NovaPrime18/nitride-nano/firmware/src/board.rs

//! Board constants and analog scaling (tune at bring-up).

/// Supply electrical limits (design targets).
pub const VOUT_MAX_MV: u32 = 60_000;
pub const VOUT_MIN_MV: u32 = 0;
pub const IOUT_MAX_MA: u32 = 20_000;
pub const POWER_MAX_MW: u32 = 240_000;

/// Input bus limits, supervised from the INA228 (rev2 input-side monitor).
/// These sit outside the PD contract itself and act as a firmware backstop on
/// top of the INA228 ALERT → SWITCH_EN hardware protection. The current limit
/// used at runtime is the active PD contract cap plus a small margin, falling
/// back to `IIN_MAX_MA` on a non-PD (XT90) input.
pub const VIN_MAX_MV: u32 = 58_000;
pub const IIN_MAX_MA: i32 = 22_000;
/// Headroom above the negotiated input-current cap before an input-overcurrent
/// fault is latched (covers measurement noise and transients).
pub const IIN_MARGIN_MA: i32 = 500;

/// NTC thermistor settings (matches PD240W-Firmware-example).
/// Circuit: 3.3V → R_PULLUP (4.7k) → NTC → GND, voltage at junction.
pub const NTC_BETA: f32 = 3950.0;
pub const NTC_R25_OHM: f32 = 10_000.0;
pub const NTC_PULLUP_OHM: f32 = 4_700.0;
pub const NTC_OVERTEMP_C: i32 = 80;
// TODO(dead-code): derating threshold carried over from the PD240W example, but no
// thermal-derating logic exists in this firmware yet, so nothing reads it.
// Preserved for when graduated derating is implemented.
// pub const NTC_DERATE_START_C: i32 = 70;

// TODO(dead-code): graduated temperature thresholds from the PD240W example AppConfig.
// Only NTC_OVERTEMP_C is actually enforced (see control::supply); these graduated
// levels are never referenced. Preserved for a future UI/derating feature.
// pub const TEMP_CAUTION_C: i32 = 50;
// pub const TEMP_WARNING_C: i32 = 65;
// pub const TEMP_CRITICAL_C: i32 = 75;
// pub const TEMP_SHUTDOWN_C: i32 = 80;

/// ADC full-scale reference (VREF+ = VDDA unless VREFBUF used for DAC only).
pub const ADC_VREF_MV: u32 = 3300;
// TODO(dead-code): misleading leftover — all ADCs run at 12-bit resolution and every
// scaling path in `sense::adc_sense` divides raw counts by 4096. Nothing references
// this 16-bit "oversampled" constant.
// pub const ADC_MAX: u32 = 65535; // 16-bit oversampled

/// Divider ratios: physical = adc_counts * SCALE / 4096 (12-bit ADC)
/// TODO: derive from Converter.kicad_sch resistor networks.
pub const VOUT_SENSE_NUM: u32 = 85_140; // mV at full scale (248k/10k divider, 3.3V ref)
/// ISMON monitor gain at the PA3 node, in mV per amp. The LT8390A datasheet
/// gives `V_ISMON = 10 · V(ISP−ISN) + V_OFFSET`, and the board's output-current
/// shunt is R18 = 2 mΩ, so the gain is `10 · 2 mΩ = 20 mV/A`. This is a
/// datasheet-derived value, not a per-board trim: verify it against a known load
/// (a shunt swap scales it directly) before changing it.
pub const ISENSE_MV_PER_A: u32 = 20;

/// Zero-current ISMON voltage at the PA3 node, in mV — the per-board offset
/// calibration.
///
/// The LT8390A offset is only specified to 0.20–0.30 V while the current signal
/// is 20 mV/A, so the full 100 mV spread is 5 A of error. Even the 5 mV residual
/// left by a near-typical part is 0.25 A on the display at *every* load — which
/// is what the 2026-09-25 bench run showed (readings low by ~0.25 A from 0.25 A
/// to 2.5 A).
///
/// MEASURE IT WITH THE OUTPUT **ENABLED** AND NO LOAD. The LT8390A's ISMON
/// buffer is powered down with the rest of the chip while `EN/UVLO` is low, so
/// the level read with the converter parked is not the operating offset. The
/// previous firmware learned the zero at boot with the converter disabled; that
/// is why the calibration never took. This constant replaces that learn.
///
/// Bench procedure: enable the output with no load, read the `isense:` RTT line
/// (`raw … mV`), or DMM the ISMON node / R49, and set this to that value. The
/// value below was fitted from the 2026-09-27 bench run: with the converter
/// enabled and no load, PA3 read raw 307–308 counts = 247–248 mV on this board,
/// so the previous 244 mV constant showed ~200–250 mA at true zero and carried
/// that offset up through the whole range.
pub const ISENSE_ZERO_MV: u32 = 248;
pub const VBUS_SENSE_NUM: u32 = 69_600;

/// DAC 12-bit. The DAC reference is VREF+, which this board ties to +3V3 (the
/// internal VREFBUF is left high-impedance in `main`), so the full-scale
/// reference is the 3.3 V rail rather than the 2.5 V VREFBUF setting.
pub const DAC_MAX_CODE: u16 = 4095;
pub const DAC_VREF_MV: u32 = 3300;

/// CV feedback network (Converter sheet, U1 = LT8390A). The FB pin is a
/// current-summing node:
///
/// ```text
///   VOUT ── R19 ──┬── R20 ── GND
///                 │
///   CV_Set ─ R36 ─┴── FB
/// ```
///
/// The LT8390A regulates FB to [`CV_FB_REF_MV`] (1.000 V typ), so summing the
/// currents into FB gives the open-loop (inverted) control law
///
/// ```text
///   V_OUT = CV_FB_REF_MV·(1 + R19/R36 + R19/R20) − V_DAC·(R19/R36)
/// ```
///
/// with `V_DAC = DAC_VREF_MV · code / DAC_MAX_CODE`. These resistor values are
/// the source of truth for the CV map — `control::dac_cv` derives the
/// setpoint→code mapping from them analytically. (A previous hand-entered
/// calibration table did not match this network: it assumed ~13.5 mV/code while
/// the network gives ~28.8 mV/code, so the real output tracked ~1.9× the
/// setpoint with an offset.)
pub const CV_FB_REF_MV: u32 = 1_000; // LT8390A FB regulation (1.00 V typ)
pub const CV_FB_TOP_OHM: u32 = 357_000; // R19, VOUT → FB
pub const CV_FB_BOTTOM_OHM: u32 = 10_000; // R20, FB → GND
pub const CV_SUM_OHM: u32 = 10_000; // R36, CV_Set → FB

/// Max CV DAC code change per supply tick (see `control::dac_cv::CvDac::slew`).
/// The supply tick is 1 ms, so this is N LSB per ms (~N*1000 LSB/s). Tune down
/// for a gentler ramp if output-stage ringing/FET heating persists.
pub const CV_SLEW_MAX_LSB_PER_TICK: u16 = 4;

/// How often the supply supervisor prints its consolidated `supply:` diagnostic.
/// One second gives a slow enough scroll to read while still catching a fault or
/// mode change within a second of the event; edge-triggered events (faults, a
/// binding power cap, a CV↔CC transition) are logged immediately regardless.
pub const SUPPLY_LOG_MS: u64 = 1_000;

/// Supply-snapshot period while the output is out of regulation (below
/// [`VOUT_SAG_PCT`] of the setpoint). A converter saturation/collapse can be
/// short-lived, so the 1 s cadence misses the interesting part; this tightens it
/// and a dedicated edge line records the transition either way.
pub const SUPPLY_LOG_SAG_MS: u64 = 200;

/// An enabled output below this percentage of its setpoint is reported as a CV
/// regulation failure (the LT8390A is not holding FB at 1 V), as opposed to a
/// deliberate current limit.
pub const VOUT_SAG_PCT: u32 = 85;

/// Advisory threshold on the commanded step-down ratio `VIN/VOUT`, in percent.
///
/// The 2026-09-27 bench run showed this board cannot hold regulation above
/// roughly 70 W when run at 48 V in / 12 V out (`VIN/VOUT = 4.0`) — it sags and
/// "chitters" — while the *same* hardware reached its full 10 A programmed CC
/// limit at 28 V in (`VIN/VOUT = 2.3`). That is the high-step-down / low-duty
/// corner (1 MHz from R1 = 147 k, with a 2.2 µH inductor and the LSP/LSN filter
/// as built). A one-shot `supply:` warning is emitted above this ratio so a
/// marginal rail is visible in the log instead of looking like a firmware bug.
/// Prefer the lowest PD rail that is still a clean buck (`control::auto_track`
/// already does this in Auto mode).
pub const DEEP_BUCK_WARN_RATIO_PCT: u32 = 300;

/// The measured output current must exceed the commanded limit by this much
/// before the software over-current fault latches. The ISMON path is only
/// specified to ±3 %, its offset is part-specific (see `ISENSE_ZERO_MV`), and
/// the observed bias on the bench was ~0.6 A — which is >5 % of a 3 A limit.
/// The hardware CC loop is the primary limit; this is a runaway backstop, so a
/// generous margin is correct. 115 % still sits below the 20 A design cap for
/// every limit below ~17 A and the absolute `IOUT_MAX_MA` check covers the top.
pub const IOUT_TRIP_MARGIN_PCT: u32 = 115;

// ---------------------------------------------------------------------------
// LT8390A output-current-limit input (CTRL pin) network
// ---------------------------------------------------------------------------
//
// The CC DAC does NOT drive the LT8390A CTRL pin directly. On the board,
//
//     PA6 / CC_Set ── R48 ──┬── CTRL (U1 pin 10)
//                           │
//     LT8390A VREF ── R5 ───┤
//                           │
//                          R4
//                           │
//                          GND
//
// so CTRL is a resistor-summing node:
//
//     V_CTRL = k · V_DAC + V_ctrl0
//     k       = (R4 || R5) / (R48 + (R4 || R5))
//     V_ctrl0 = VREF · R4 / (R4 + R5)
//
// `control::dac_cc` inverts this to turn a requested current limit into a DAC
// code (and reports the limit a code actually produces), and `control::supply`
// logs both so a divider mismatch is visible instead of silent.
//
// NOTE (rev2 fitted values): R48 = 10 k, R5 = 357 k, R4 = 75 k. R5 was raised
// from 124 k to 357 k as the "DAC high-Z / MCU held in reset" fail-safe: with
// the DAC floated, V_CTRL = VREF·R4/(R4+R5) ≈ 0.347 V, i.e. ≈ 4.9 A, instead of
// ≈ 25 A with 124 k. **If the next board revision changes this divider, update
// these three constants or every CC limit will be wrong.**
pub const LT8390_VREF_MV: u32 = 2_000; // LT8390A VREF pin (NOT the 1.0 V FB ref)
pub const CTRL_SERIES_OHM: u32 = 10_000; // R48, CC_Set → CTRL
pub const CTRL_VREF_OHM: u32 = 357_000; // R5,  VREF    → CTRL
pub const CTRL_GND_OHM: u32 = 75_000; // R4,  CTRL    → GND

/// LT8390A CTRL→current-limit transfer, from the datasheet:
///
/// ```text
///   V(ISP−ISN)_threshold = (V_CTRL − 0.25 V) · 0.1     (0.3 V ≤ V_CTRL ≤ 1.15 V)
///   I_LIMIT              = V(ISP−ISN)_threshold / R18
/// ```
///
/// so with the R18 = 2 mΩ output shunt, `I_LIMIT(mA) = (V_CTRL(mV) − 250) · 50`.
/// The transfer saturates at `V_CTRL ≥ 1.35 V` (100 mV ⇒ 50 A) and the part
/// latches switching off below [`LT8390_CTRL_LATCHOFF_MV`] — which is why the
/// disabled path's CC code of 0 is a genuine shutdown, not just a low limit.
pub const LT8390_CTRL_OFFSET_MV: u32 = 250;
/// Sense-threshold volts per volt of CTRL, scaled ×1000 (0.1 V/V).
pub const LT8390_CTRL_SLOPE_MILLI: u32 = 100;
/// Output current shunt R18, in milliohms.
pub const ISENSE_SHUNT_MOHM: u32 = 2;
/// Below this CTRL voltage the LT8390A stops switching (latch-off, 285–315 mV).
pub const LT8390_CTRL_LATCHOFF_MV: u32 = 300;

// ---------------------------------------------------------------------------
// Achievable CC-limit range (the part's CTRL window, not the firmware's choice)
// ---------------------------------------------------------------------------
//
// The datasheet's CTRL → ISP/ISN threshold transfer is three regions:
//
//   0.30 V ≤ V_CTRL ≤ 1.15 V   linear,  threshold 5 mV → 90 mV
//   1.15 V ≤ V_CTRL ≤ 1.35 V   smooth transition 90 mV → 100 mV
//           V_CTRL ≥ 1.35 V   constant 100 mV full scale
//           V_CTRL < 0.30 V   stops switching (latch-off)
//
// so the part can command a **20:1** current window (5 → 100 mV), and no single
// shunt value can reach below `CC_MIN_MA`. With the fitted R18 = 2 mΩ that is
// 2.5 A … 50 A. The low end sits exactly on the latch-off, hence the settable
// floor below.

/// Sense-threshold window endpoints, in mV across R18.
pub const LT8390_CTRL_MIN_SENSE_MV: u32 = 5;
pub const LT8390_CTRL_LINEAR_MAX_SENSE_MV: u32 = 90;
pub const LT8390_CTRL_MAX_SENSE_MV: u32 = 100;
/// CTRL voltages where the window is linear-top / saturated, in mV.
pub const LT8390_CTRL_LINEAR_TOP_MV: u32 = 1_150;
pub const LT8390_CTRL_SAT_MV: u32 = 1_350;

/// Smallest / largest current limit the fitted shunt can **sustain** (`mV/mΩ = A`,
/// so `sense_mV · 1000 / R18_mΩ` is mA). With R18 = 2 mΩ: 2.5 A … 50 A. The low
/// end is the exact latch-off and is only reachable once the stage is already
/// switching — see [`CC_SET_MIN_MA`] for the cold-start floor.
pub const CC_MIN_MA: u32 = LT8390_CTRL_MIN_SENSE_MV * 1_000 / ISENSE_SHUNT_MOHM;
pub const CC_MAX_MA: u32 = LT8390_CTRL_MAX_SENSE_MV * 1_000 / ISENSE_SHUNT_MOHM;

/// CTRL voltage needed to *leave* latch-off: the falling-threshold worst case
/// (315 mV) plus the 25 mV hysteresis.
///
/// This is the trap in the low end of the CC range. The part can *sustain* a
/// limit down at `LT8390_CTRL_LATCHOFF_MV` (0.30 V → 2.5 A) **once it is
/// switching**, but from a cold start it will not begin switching until CTRL
/// exceeds ~0.34 V. That is why the 2026-09-28 CV run held ~2.5 A while a CC
/// cold start would not hold below ~6 A — start-vs-sustain, not a map error.
pub const LT8390_CTRL_LATCHOFF_MAX_MV: u32 = 315;
pub const LT8390_CTRL_LATCHOFF_HYST_MV: u32 = 25;
pub const LT8390_CTRL_START_MV: u32 =
    LT8390_CTRL_LATCHOFF_MAX_MV + LT8390_CTRL_LATCHOFF_HYST_MV;
/// Datasheet-guaranteed cold-start floor (`(340 − 250) mV / 2 mΩ` = 4.5 A).
pub const CC_START_MIN_MA: u32 =
    (LT8390_CTRL_START_MV - LT8390_CTRL_OFFSET_MV) * 100 / ISENSE_SHUNT_MOHM;

/// Bench-measured CC current offset: near the low end the loop delivers this
/// much *more* current than commanded. On the 2026-09-28 board, setting 0.1 A
/// drew 3.75 A and 0.2 A drew 3.85 A — a clean 1:1 slope with a **+3.65 A
/// intercept**, i.e. a CTRL / ISP-ISN offset near latch-off, not a DAC map
/// error. `dac_cc` cancels it here so the number on the I-LIM screen is the
/// current actually drawn. Re-measure at mid-range before trusting it across
/// the whole range: a 10 A run on 2026-09-27 tracked to <1 %, so the offset is
/// known to fade at high current.
pub const CC_CURRENT_OFFSET_MA: u32 = 3_650;

/// Settable CC-range floor: the offset above plus a 0.1 A command, so the lowest
/// setting (3.75 A here) is the lowest current the loop can actually deliver.
/// Because the setpoint now means the *actual* current, the range reads
/// 3.75 A … 20 A rather than 0.1 A … 20 A.
pub const CC_SET_MIN_MA: u32 = CC_CURRENT_OFFSET_MA + 100;
/// Settable CC-range ceiling (design max; the chip itself would allow 50 A).
pub const CC_SET_MAX_MA: u32 = IOUT_MAX_MA;

/// I2C addresses
pub const TPS26750_ADDR: u8 = 0x21;
pub const SSD1306_ADDR: u8 = 0x3C;
pub const CAT24C512_ADDR: u8 = 0x50;
/// INA228 input power monitor on the PD bus (A0 = A1 = GND).
pub const INA228_ADDR: u8 = 0x40;

/// INA228 scaling. R60 = 8 mΩ on the input bus; 20 A × 8 mΩ = 160 mV, which
/// fits the ±163.84 mV `ADCRANGE = 0` shunt range with ~2 % headroom.
pub const INA228_SHUNT_MOHM: u32 = 8;
pub const INA228_MAX_CURRENT_MA: u32 = IOUT_MAX_MA;
/// CONFIG: ADCRANGE = 0 (±163.84 mV), shunt temperature compensation off.
pub const INA228_CONFIG: u16 = 0x0000;
/// ADC_CONFIG: MODE = 0xF (continuous bus + shunt + temperature), 1052 µs per
/// conversion, AVG = 16 → ~50 ms per full update. Sample it every 100 ms.
pub const INA228_ADC_CONFIG: u16 = 0xFB6A;
/// SHUNT_CAL = 13107.2e6 × CURRENT_LSB × R_shunt with
/// CURRENT_LSB = 20 A / 2^19 = 38.147 µA and R_shunt = 8 mΩ → 4000.
pub const INA228_SHUNT_CAL: u16 = 4_000;

/// Auto-tracking PD rail selection.
///
/// The LT8390A only leaves its 4-switch buck-boost region when `VIN/VOUT` is at
/// least ~1.33 (clean buck) or at most ~0.75 (clean boost); the peak-buck/peak-
/// boost crossover sits at 0.98–1.04. These percentages add a small guard band
/// on top of the datasheet typical thresholds. They are the tuning knobs for
/// the bench efficiency sweep: lower them to allow rails closer to the
/// transition, raise them for more margin.
pub const AUTO_TRACK_BUCK_MIN_RATIO_PCT: u32 = 135;
pub const AUTO_TRACK_BOOST_MAX_RATIO_PCT: u32 = 70;
/// Delivered-power headroom required of a candidate rail before it is accepted
/// (`rail_mw >= requested_mw * pct / 100`), covering conversion losses.
pub const AUTO_TRACK_POWER_HEADROOM_PCT: u32 = 110;
/// A setpoint must be stable this long before a rail change is commanded, and
/// two rail changes are never closer together than the interval below.
pub const AUTO_TRACK_SETTLE_MS: u64 = 300;
pub const AUTO_TRACK_MIN_INTERVAL_MS: u64 = 1_000;
/// Park the converter while the input rail is renegotiated. The LT8390A copes
/// with VIN steps, but a PD source can momentarily drop VBUS to 5 V during a
/// re-request, so the output is briefly disabled to protect the stage.
pub const AUTO_TRACK_DISABLE_DURING_SWITCH: bool = true;

/// Highest SPR contract voltage. A rail above this can only be obtained by
/// entering EPR mode; the TPS26750 attempts EPR on its own once a request
/// window above this is allowed and the loaded sink configuration declares EPR
/// PDOs. Keep in step with `0x33` / `0x37` of `config_TPS26750_*_fullFlash.c`.
pub const SPR_MAX_MV: u32 = 20_000;
/// Fixed EPR rails the sink configuration declares (`0x33` PDOs 8-10). The
/// source's own EPR PDOs are invisible in `RX_SOURCE_CAPS` until EPR mode has
/// been entered, so [`crate::pd::auto_track`] injects these as candidates when
/// the output setpoint cannot be served from SPR alone.
pub const EPR_RAILS_MV: [u32; 3] = [28_000, 36_000, 48_000];
/// Current assumed for an injected EPR rail (EPR fixed PDOs carry 5 A).
pub const EPR_RAIL_CURRENT_MA: u32 = 5_000;
/// EPR AVS APDO window declared by the sink configuration (`0x33` PDO 11).
///
/// Before EPR mode has been entered, an above-SPR rail is requested as an **EPR
/// AVS** contract inside this window: asserting `EPR AVS Enable Sink Mode`
/// (0x37 bit 128) is what makes the controller attempt EPR mode entry (TRM
/// Table 4-21), and SDAA265 §5.3 makes a bare fixed >20 V window fall back to
/// 5 V. Once EPR is entered and the source advertises its own EPR PDOs, a
/// specific above-SPR preset is requested as a **fixed** EPR PDO through
/// `Tps26750::request_fixed_epr_rail` instead (see `PD_ROOT_CAUSE.md`).
/// Keep in step with `0x33`/`0x37` of the config image.
pub const EPR_AVS_MIN_MV: u32 = 15_000;
pub const EPR_AVS_MAX_MV: u32 = 48_000;

/// How long to keep the converter output disabled after an EPR request before
/// loading it. Some sources are still settling VBUS through the 20→28/48 V
/// transition; enabling the load then can dip VBUS enough to brown the board
/// out. Two chargers did this at 28 V while a powerbank at the same voltage did
/// not, so this is a ride-through window, not a fixed voltage limit.
pub const EPR_SETTLE_MS: u64 = 800;
/// USB-PD SPR PPS is only defined inside this window; a manual preset that
/// lands here with no matching fixed PDO is served by a PPS contract.
pub const PPS_MIN_MV: u32 = 3_300;
pub const PPS_MAX_MV: u32 = 21_000;
/// A preset this close to a fixed PDO uses the fixed PDO instead of PPS.
pub const PPS_FIXED_PREFER_MV: u32 = 1_000;

/// Converter disable: active level (verify on bench vs LT8390 RUN).
pub const CONVERTER_DISABLE_ACTIVE_HIGH: bool = true;

/// UI timing
pub const DEBOUNCE_MS: u64 = 25;
/// Max gap between two encoder-button presses that counts as a double click.
/// The single-click action (VSET mode on the Main screen) is deferred by this
/// long so a double click can be recognised instead; it comfortably exceeds
/// `DEBOUNCE_MS` while staying short enough that entering VSET mode still feels
/// immediate.
pub const ENC_DOUBLE_CLICK_MS: u64 = 350;
/// Quadrature counts per encoder detent. `Qei::new` configures the timer for
/// X4 decoding (`Sms::ENCODER_MODE_3`). The fitted encoder produces a detent
/// every two counts (measured: one detent used to fire two `EncTurn` events, and
/// dividing by 4 made the knob half-speed). Raw counts are divided by this so
/// every screen receives one event per detent.
pub const ENCODER_COUNTS_PER_DETENT: i32 = 2;
pub const UI_REFRESH_MS: u64 = 80;
pub const INPUT_POLL_MS: u64 = 5;
pub const SUPPLY_TICK_MS: u64 = 1;
pub const ADC_SAMPLE_MS: u64 = 2;
/// INA228 refresh period. Must be longer than the chip's ~50 ms conversion
/// cycle (ADC_CONFIG above) or reads return overlapping samples.
pub const INA228_POLL_MS: u64 = 100;

// ---------------------------------------------------------------------------
// Status LED (D31 on PA15)
// ---------------------------------------------------------------------------

/// Status LED wiring: `PA15 → D31 (anode → cathode) → R81 → GND`, so PA15
/// HIGH lights it — **active high**. PA15 is `TIM2_CH1`; TIM2 is otherwise
/// unused (TIM4 is the encoder QEI, TIM15 is the Embassy time driver), so the
/// LED is driven as hardware PWM and can be dimmed precisely.
pub const LED_PWM_HZ: u32 = 1_000;

/// LED task tick. Only the on/off *envelope* is quantised to this; the
/// brightness inside an "on" phase is set by the PWM duty, so the heartbeat
/// stays dim and steady even at this tick rate.
pub const LED_TICK_MS: u64 = 5;

/// PWM duty for the healthy heartbeat pulses. Low enough to read as "very dim"
/// next to the full-brightness error codes — tune to taste on the bench.
pub const LED_HEARTBEAT_DUTY_PCT: u8 = 3;

/// PWM duty for fault/error code flashes (full brightness, hard to miss).
pub const LED_FAULT_DUTY_PCT: u8 = 100;

/// PWM duty for the in-progress (EEPROM activity) pulse.
pub const LED_ACTIVITY_DUTY_PCT: u8 = 35;

/// Report "INA228 missing" / "PD controller lost" / "PD no rail" as blink
/// codes. Set false to limit the LED to latched faults + EEPROM status, which
/// is what a build without those parts fitted wants.
pub const LED_SUBSYSTEM_CODES: bool = true;

/// Suppress the INA228 / PD-controller "missing" codes for this long after
/// boot. Both subsystems are probed asynchronously and are legitimately absent
/// for the first moments of a power-up, so the LED would otherwise flash a
/// code on a perfectly healthy boot.
pub const LED_SUBSYSTEM_GRACE_MS: u64 = 4_000;

/// CFG menu → "Output V sweep": 32 points evenly spaced from 10 V to 56 V,
/// inclusive at both ends (31 intervals, ≈1.48 V/step), each held for 2 s
/// (~64 s total).
///
/// NOTE: `control::dac_cv::CvDac::mv_to_code` derives its map from the FB
/// network, whose code-0 output is well above 60 V, so every sweep point is
/// reached without clamping. `VOUT_MAX_MV` is 60 V, so the supply supervisor's
/// 105 % overvoltage guard never trips on a sweep.
pub const SWEEP_START_MV: u32 = 10_000;
pub const SWEEP_END_MV: u32 = 56_000;
/// Number of points in one sweep (inclusive of both endpoints).
pub const SWEEP_POINTS: u8 = 32;
/// Dwell time per sweep point.
pub const SWEEP_STEP_MS: u64 = 2_000;

/// Sweep efficiency diagnostics: skip this much of each point's dwell before
/// accumulating anything.
///
/// The CV DAC slews at [`CV_SLEW_MAX_LSB_PER_TICK`] (4 LSB/ms ≈ 28.8 mV/code).
/// The worst case is point 0, which starts from the parked code and needs
/// ~482 ms to reach 10 V; 800 ms also covers the output capacitor and the ADC
/// telemetry EMA (tau 150 ms). The remaining 1.2 s of the dwell is the
/// measurement window.
pub const SWEEP_SETTLE_MS: u64 = 800;

/// Accumulation cadence inside the measurement window: one input/output power
/// pair every interval (a 2 s dwell gives ~60 samples).
pub const SWEEP_SAMPLE_MS: u64 = 20;

/// A point needs at least this many accepted samples to count toward the sweep's
/// best/worst summary. Below it the point is still logged but marked invalid, so
/// a stalled loop or a barely-answering INA228 cannot produce a bogus record.
pub const SWEEP_MIN_SAMPLES: u16 = 10;

/// Service mode: hand off to the ROM bootloader so the board can be reflashed
/// over UART through the on-board FT234XD (USART3, PC10/PC11).
///
/// Listener baud for the AN3155 sync byte. It MUST match the host tool's
/// connect baud (`STM32CubeProgrammer -c ... br=`, `stm32flash -b`), because
/// only the *first* byte is matched here — after the handoff the ROM loader
/// auto-bauds. STM32CubeProgrammer defaults to 115200; stm32flash to 57600.
pub const SERVICE_UART_BAUD: u32 = 115_200;

/// Watch USART3 for the bootloader sync byte (`0x7F`) and hand off when it
/// arrives. This is what makes "open the programmer and connect" just work.
pub const SERVICE_UART_AUTODETECT: bool = true;

/// Hold BTN1 through power-up (or reset) to enter service mode. Deterministic,
/// needs no UART, and doubles as the bring-up test for the handoff path.
pub const SERVICE_BOOT_HOLD: bool = true;

/// Delay after parking the output before resetting into the bootloader, giving
/// the converter time to shut down and the output to discharge.
///
/// NOTE: this covers only the moments *before* the reset. Once the MCU resets,
/// PA11 floats and Q13's gate is unconstrained, so the converter's state during
/// flashing is set by the R7/R8 divider — see the /Converter/Conv-Disable
/// finding in `BENCH.md`.
pub const SERVICE_PARK_SETTLE_MS: u64 = 100;
