NovaPrime18/nitride-nano/firmware/src/ssd1306_ui.rs

//! SSD1306 UI module for displaying status messages on the OLED display.

use embedded_graphics::{
    prelude::*,
    pixelcolor::BinaryColor,
    primitives::{Line, Rectangle},
    mono_font::{ascii::FONT_6X8, MonoTextStyleBuilder},
};
use ssd1306::{prelude::*, I2CDisplay};

/// Displays a message on the SSD1306 OLED display.
///
/// # Arguments
/// * `display` - A mutable reference to the SSD1306 display instance.
/// * `message` - The message to display.
pub fn show_message(display: &mut I2CDisplay<_, ssd1306::prelude::I2CInterface<_>>, message: &str) {
    let style = MonoTextStyleBuilder::new()
        .font(&FONT_6X8)
        .text_color(BinaryColor::On)
        .build();

    display.clear().unwrap();
    Text::with_baseline(message, Point::new(0, 12), style, Baseline::Top).draw(display).unwrap();
    display.flush().unwrap();
}
